Team-olympus-Mechatronics/Vision-Based-Robotic-System/Color detection/bandicam 2023-04-05 17-35-04-859.jpg

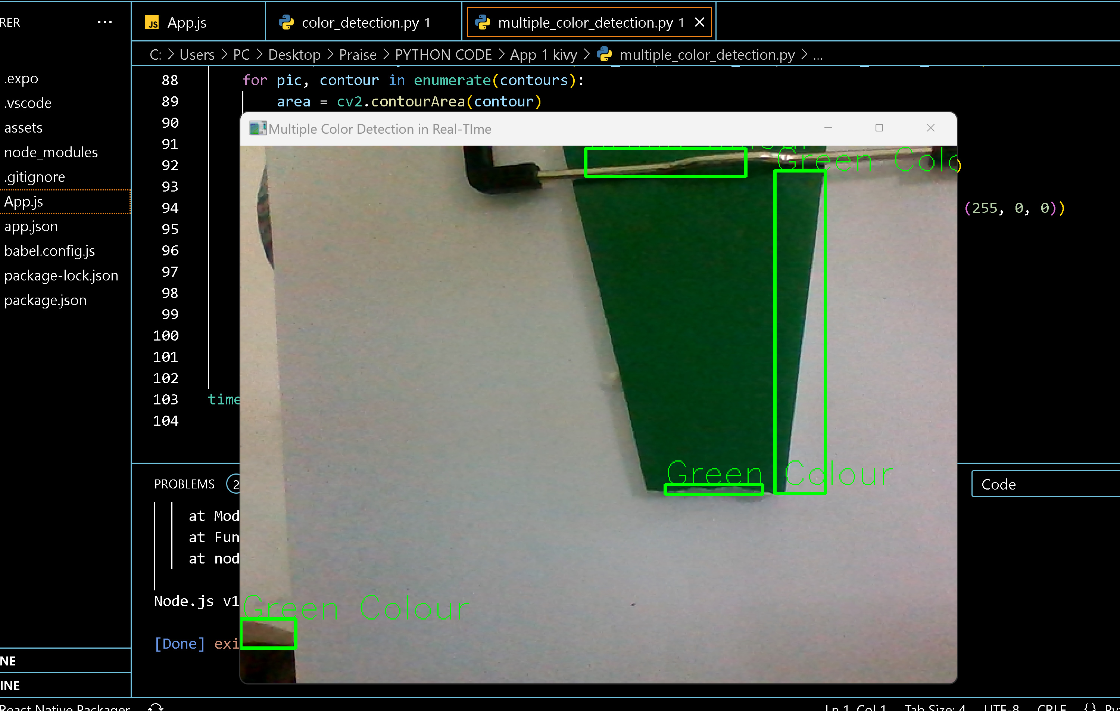
Color detection/bandicam 2023-04-05 17-35-04-859.jpg
