Team-olympus-Mechatronics/Vision-Based-Robotic-System/Robotic Arm and Sensor Controls/circuit image thinkercad.png

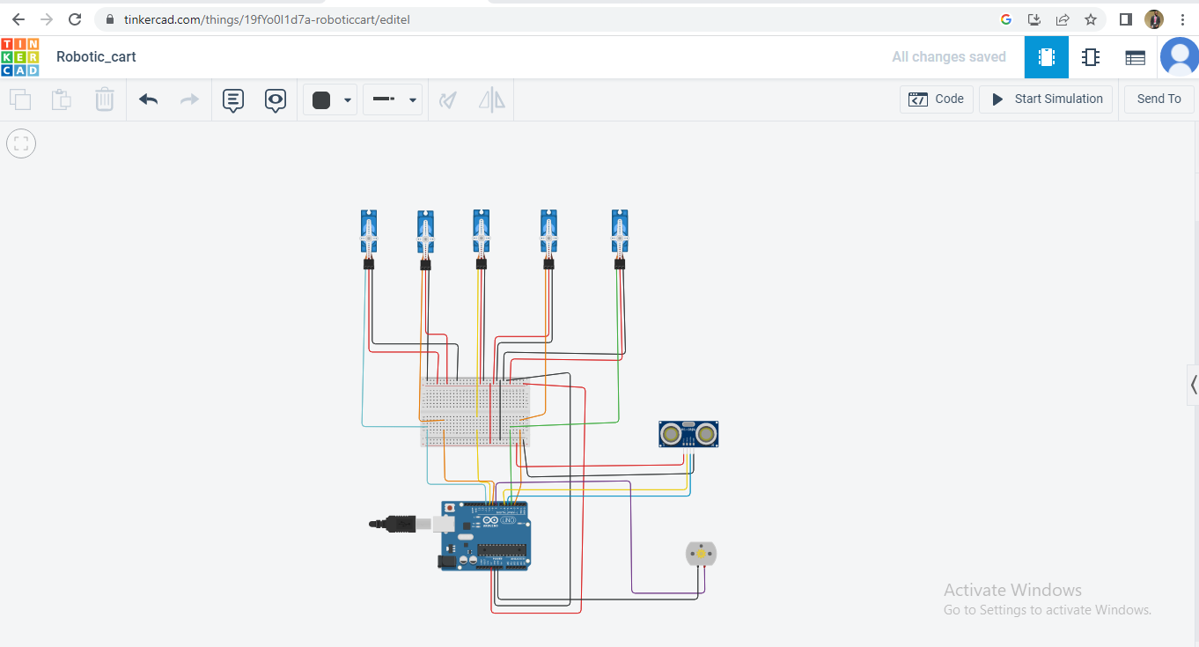
Robotic Arm and Sensor Controls/circuit image thinkercad.png
