Team-olympus-Mechatronics/Vision-Based-Robotic-System/Robotic Arm and Sensor Controls/Proteus/arduino and motor driver.png

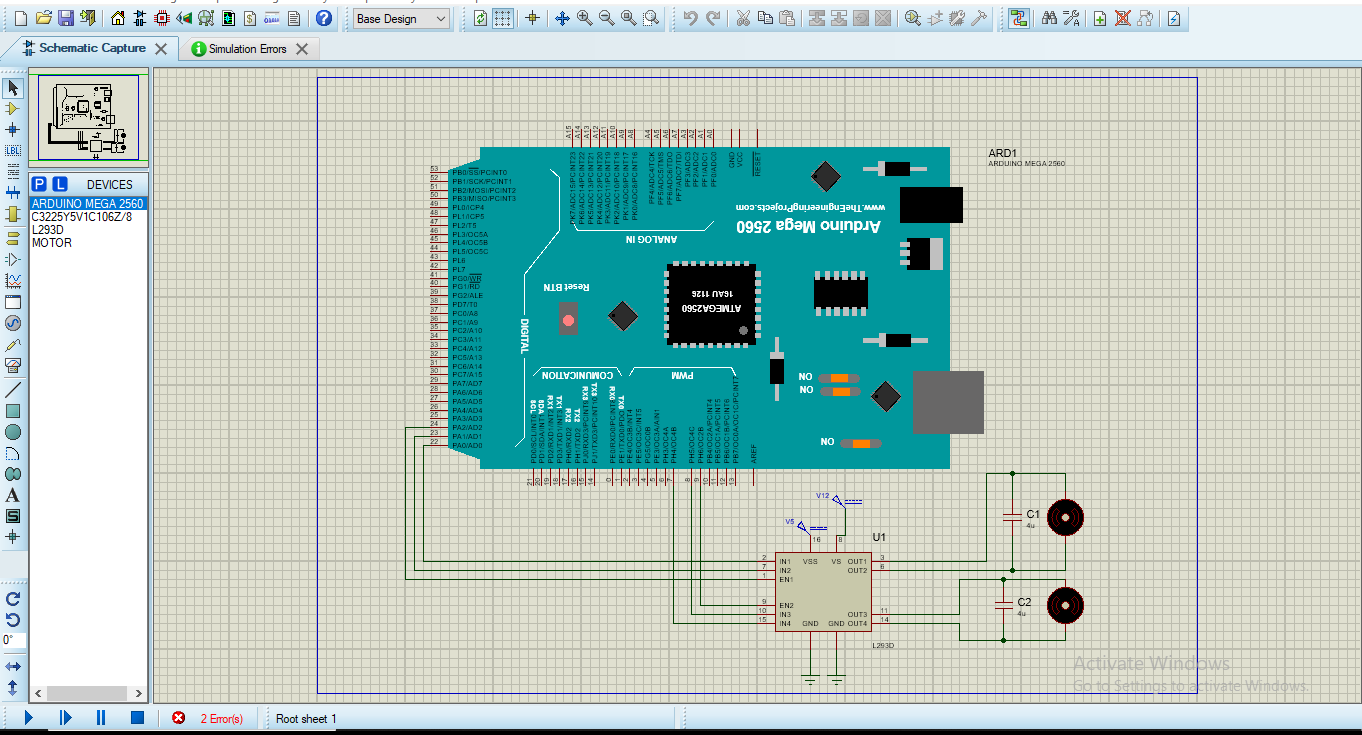
Robotic Arm and Sensor Controls/Proteus/arduino and motor driver.png
