Team-olympus-Mechatronics/Vision-Based-Robotic-System/Robotic Arm and Sensor Controls/Proteus/motor driver (1).png

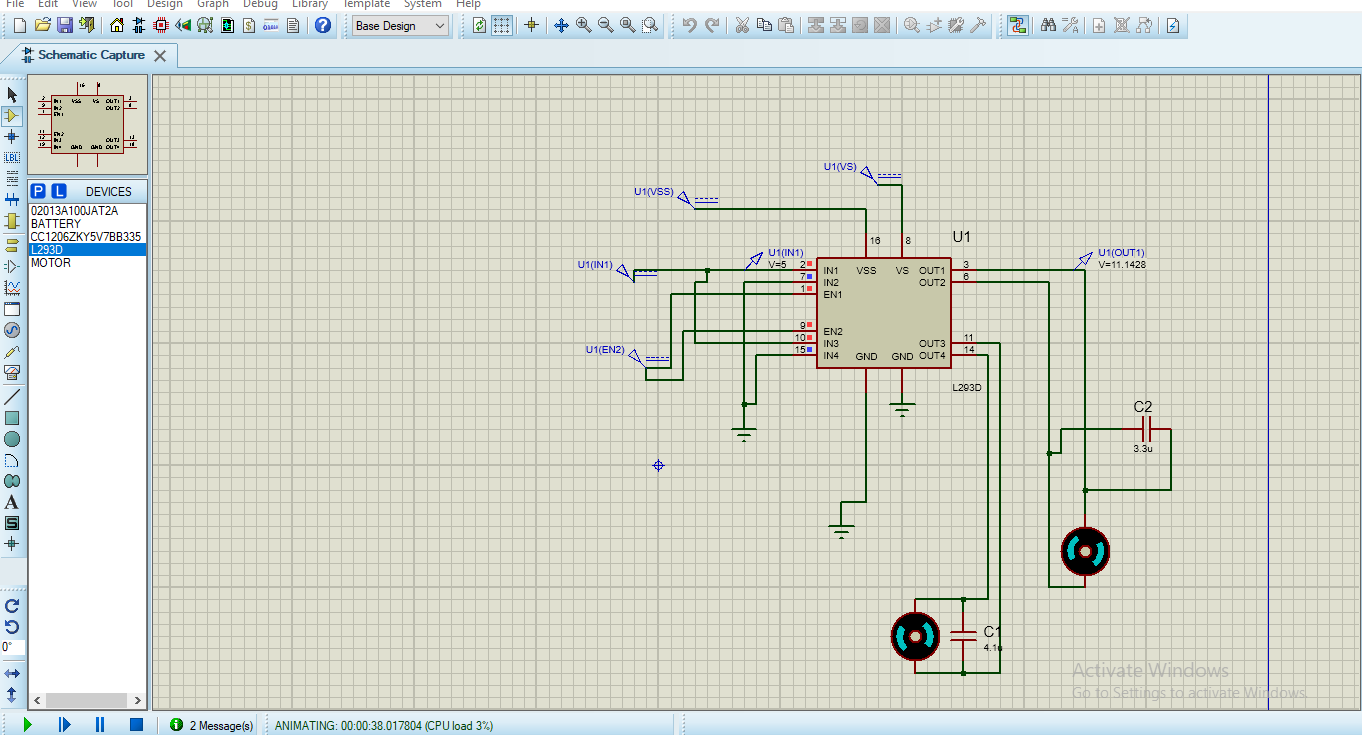
Robotic Arm and Sensor Controls/Proteus/motor driver (1).png
