Team-olympus-Mechatronics/Vision-Based-Robotic-System/Vision based robotic system 3D Modelling/Screenshots/2.png

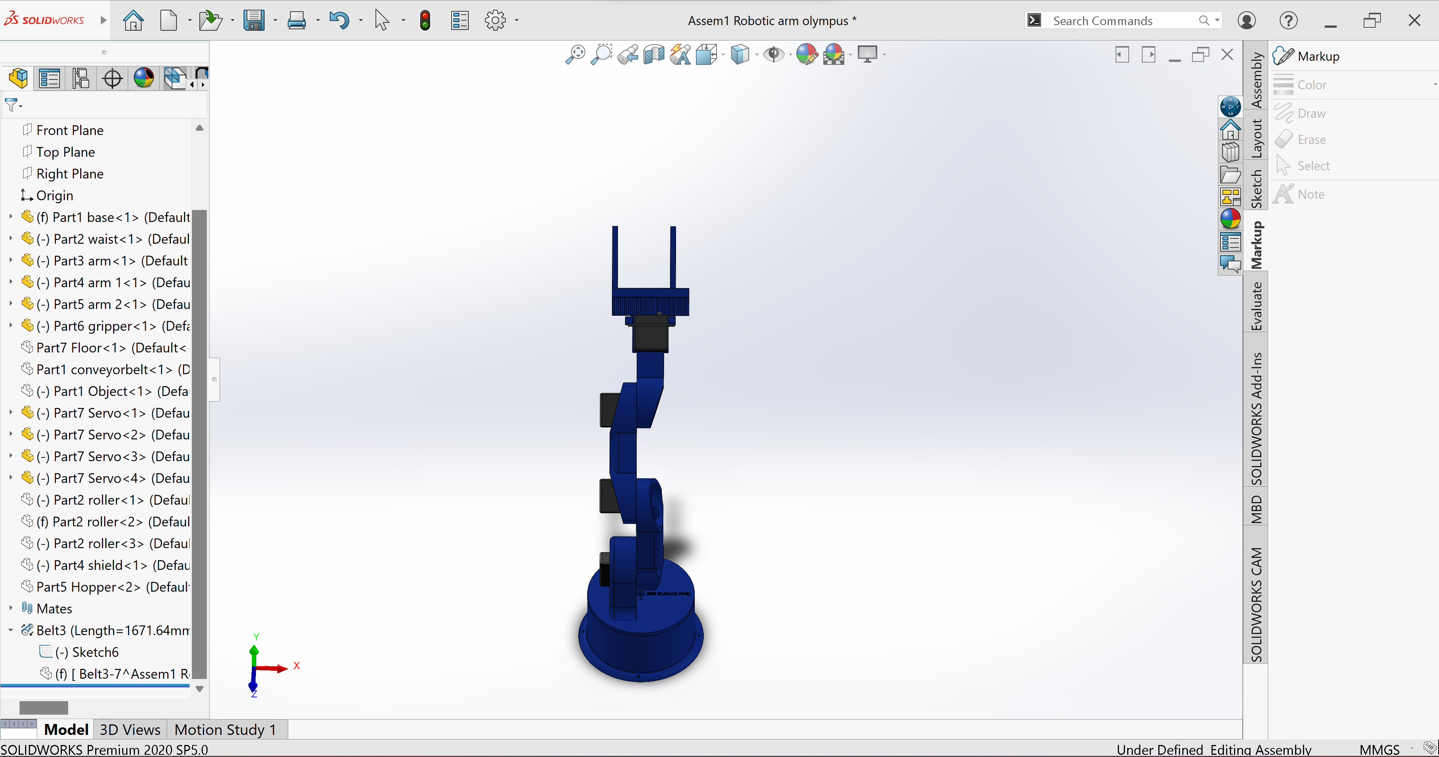
Vision based robotic system 3D Modelling/Screenshots/2.png
