Team-olympus-Mechatronics/Vision-Based-Robotic-System/Vision based robotic system 3D Modelling/Screenshots/9.png

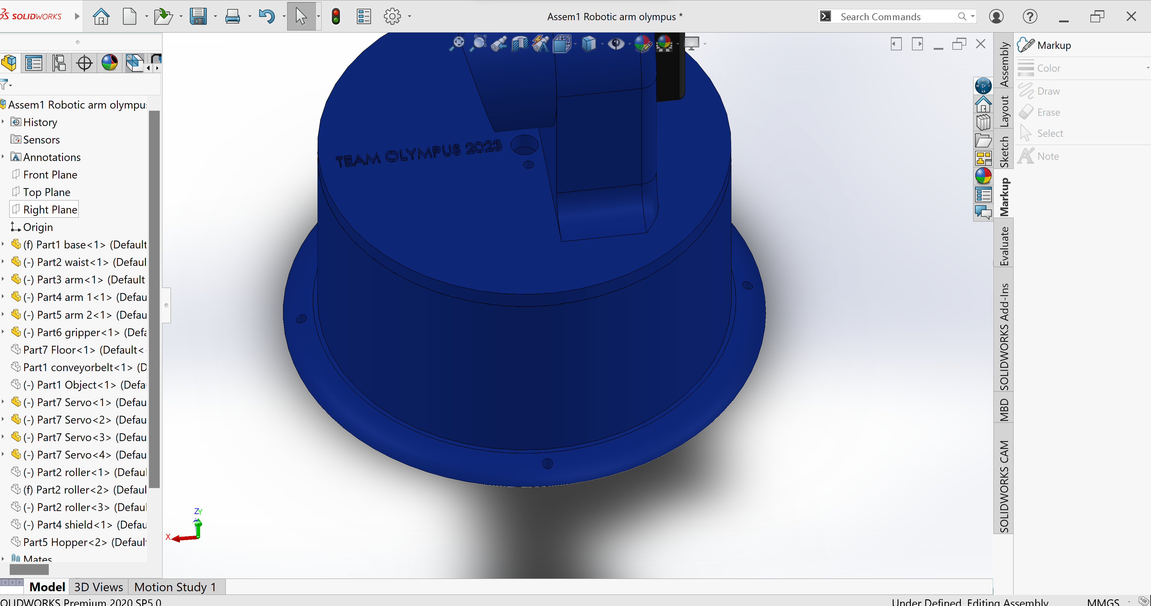
Vision based robotic system 3D Modelling/Screenshots/9.png
