Team-olympus-Mechatronics/Vision-Based-Robotic-System/Robotic Arm and Sensor Controls/components thinkercad (1).png

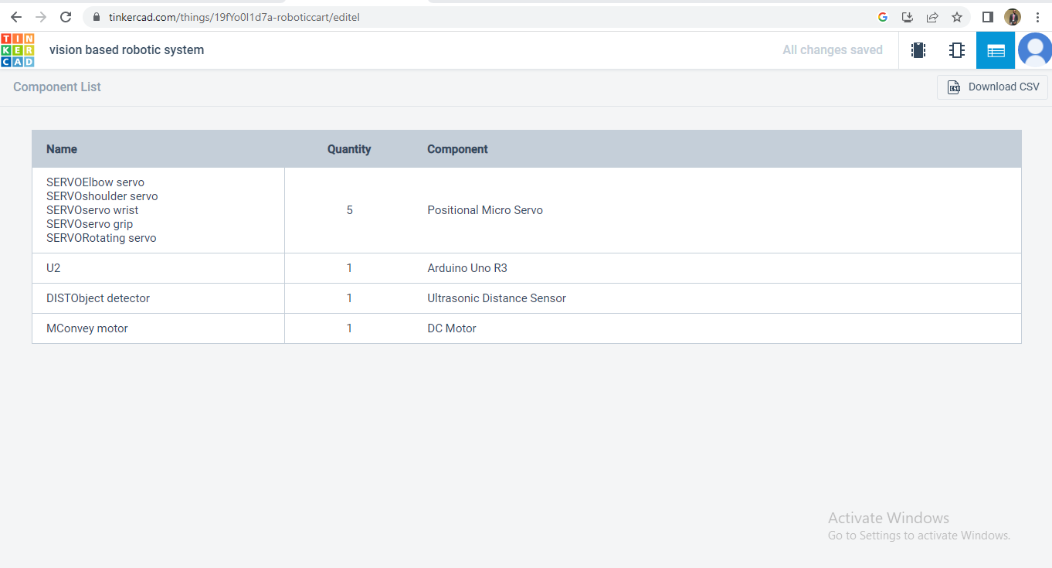
Robotic Arm and Sensor Controls/components thinkercad (1).png
